jareddonovan/creative-coding-cabinets/images/cabinet-128x128.png

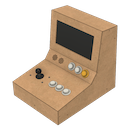
images/cabinet-128x128.png
