jareddonovan/creative-coding-cabinets/cad-files/stls/panels/top-panel.stl

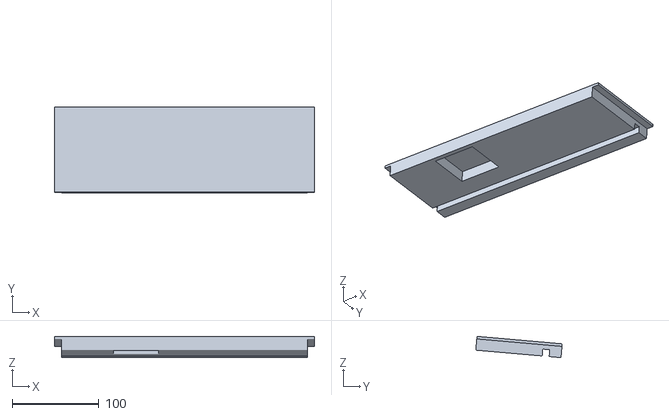
[picture p18: CAD file, 2024-05-04]
cad-files/stls/panels/top-panel.stl
300.0 x 99.8 x 24.5
