jareddonovan/creative-coding-cabinets/cad-files/stls/panels/kb-panel.stl

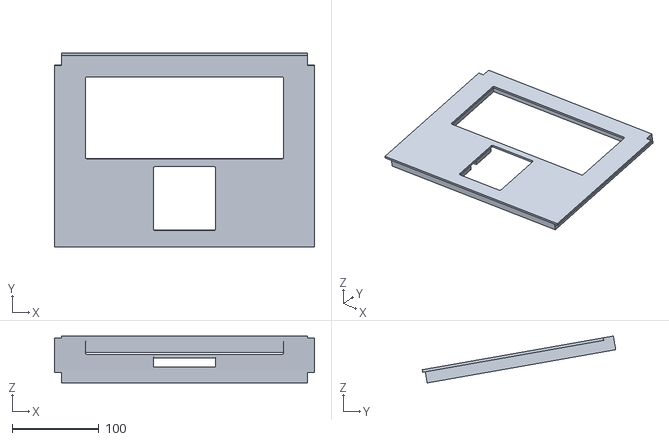
[picture p19: CAD file, 2024-05-04]
cad-files/stls/panels/kb-panel.stl
300.0 x 223.4 x 54.1
