jareddonovan/creative-coding-cabinets/cad-files/stls/panels/base-panel.stl

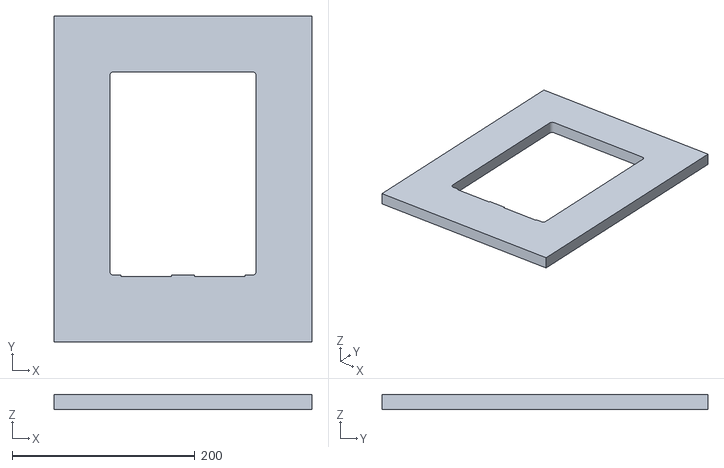
[picture p20: CAD file, 2024-05-04]
cad-files/stls/panels/base-panel.stl
282.0 x 356.0 x 16.0
