jareddonovan/creative-coding-cabinets/cad-files/stls/panels/arcade-panel.stl

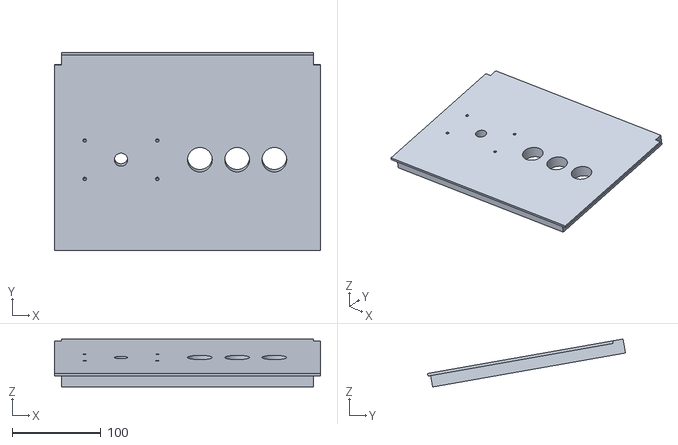
[picture p21: CAD file, 2024-05-04]
cad-files/stls/panels/arcade-panel.stl
300.0 x 223.4 x 54.1
