jareddonovan/creative-coding-cabinets/cad-files/stls/panels/back-panel.stl

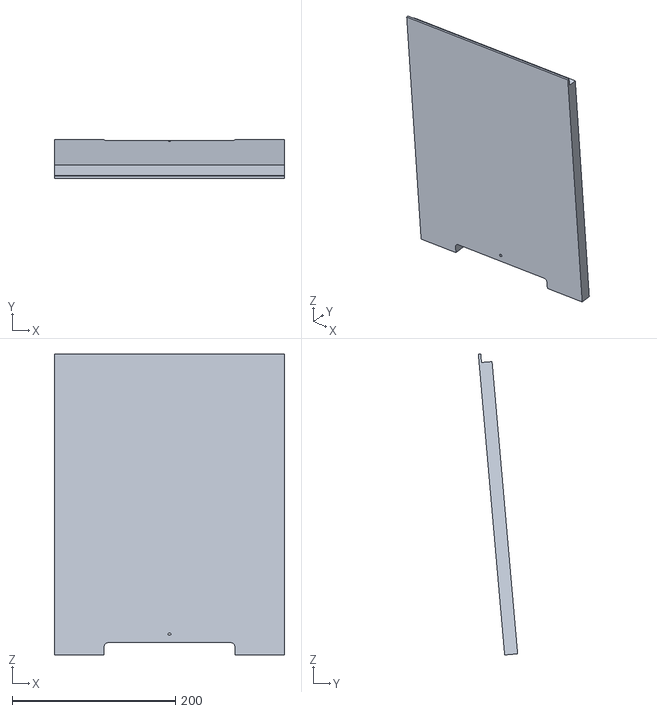
[picture p22: CAD file, 2024-05-04]
cad-files/stls/panels/back-panel.stl
282.0 x 48.1 x 368.5
