jareddonovan/creative-coding-cabinets/cad-files/stls/panels/monitor-panel.stl

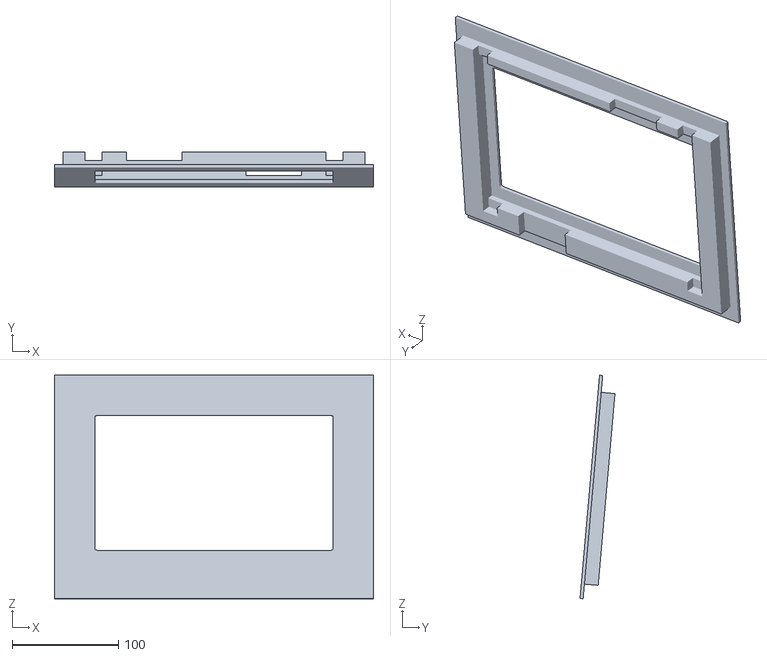
[picture p23: CAD file, 2024-05-04]
cad-files/stls/panels/monitor-panel.stl
300.0 x 32.9 x 210.4
